cristianoag/msx-mouse-ps2/images/2024-01-14_22-41_1.png

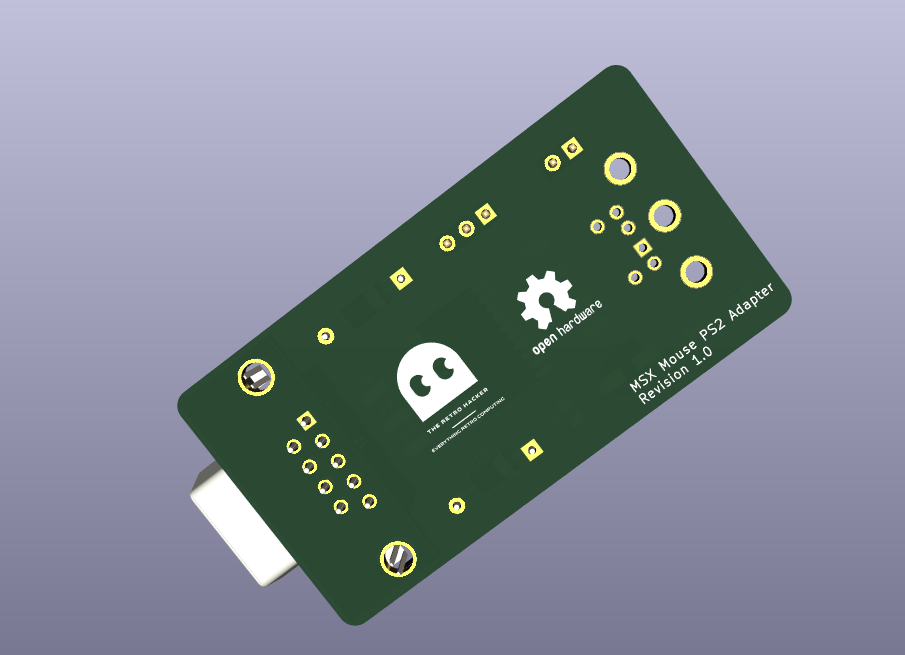
images/2024-01-14_22-41_1.png
